JQIamo/RF-Current-Source/Data/D1/D1_422Ohm_20mv_img.PNG

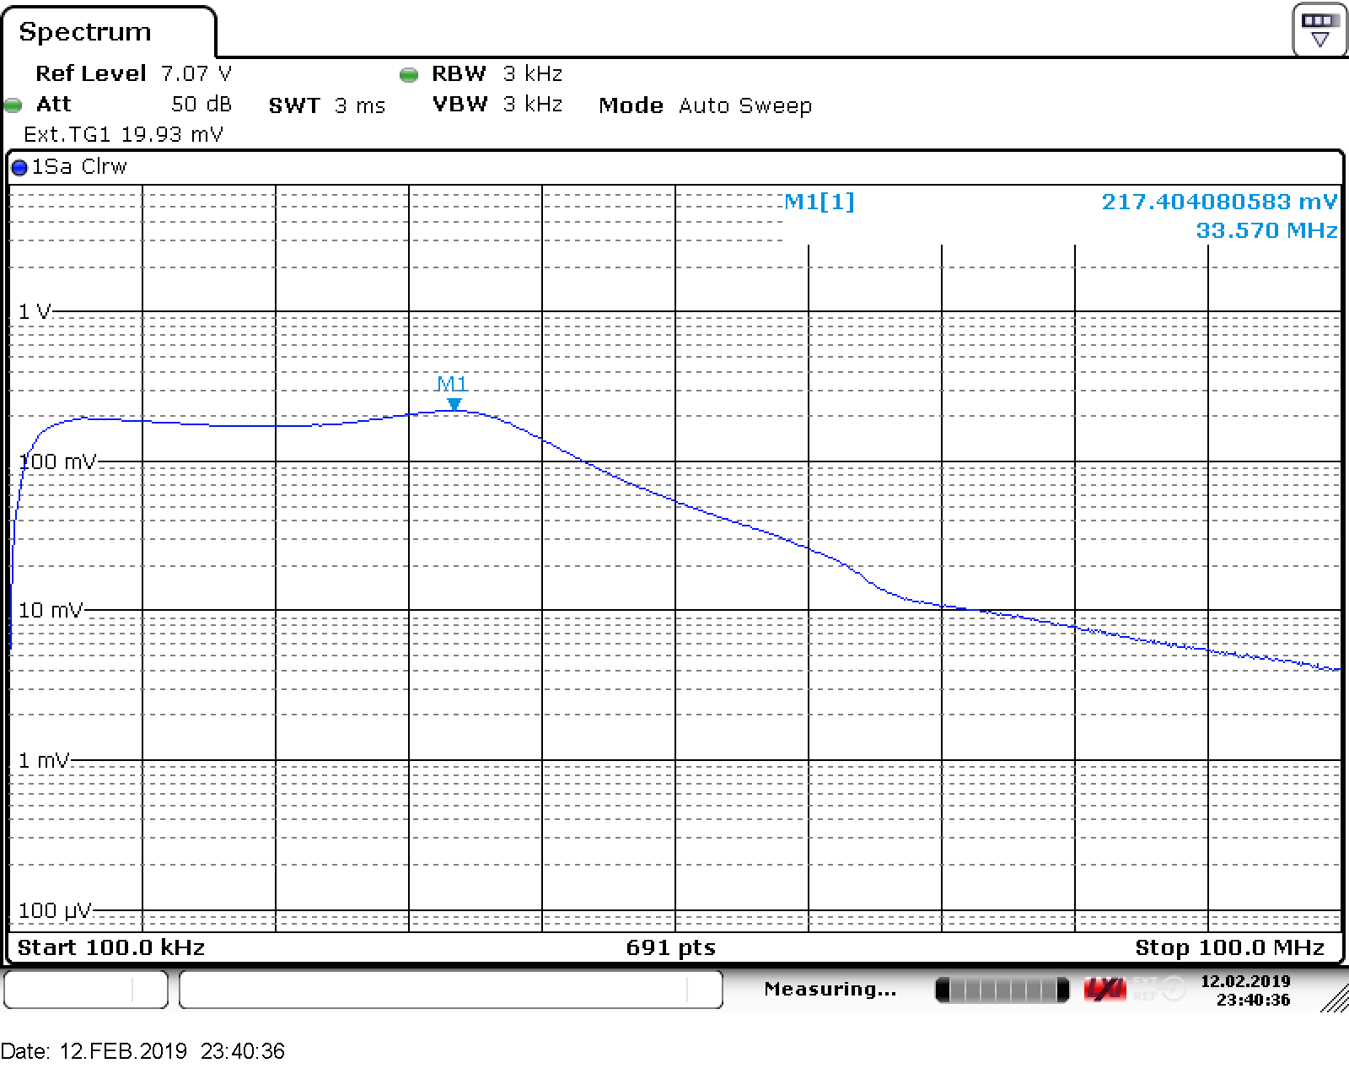
Data/D1/D1_422Ohm_20mv_img.PNG
