JQIamo/RF-Current-Source/Data/D1/D1_422Ohm_50mv_Bitter_img.JPG

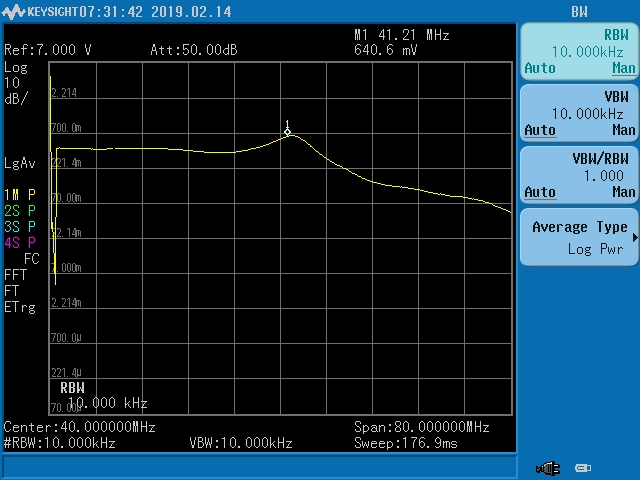
Data/D1/D1_422Ohm_50mv_Bitter_img.JPG
