JQIamo/RF-Current-Source/Data/D1/D1_422Ohm_90mv_img.PNG

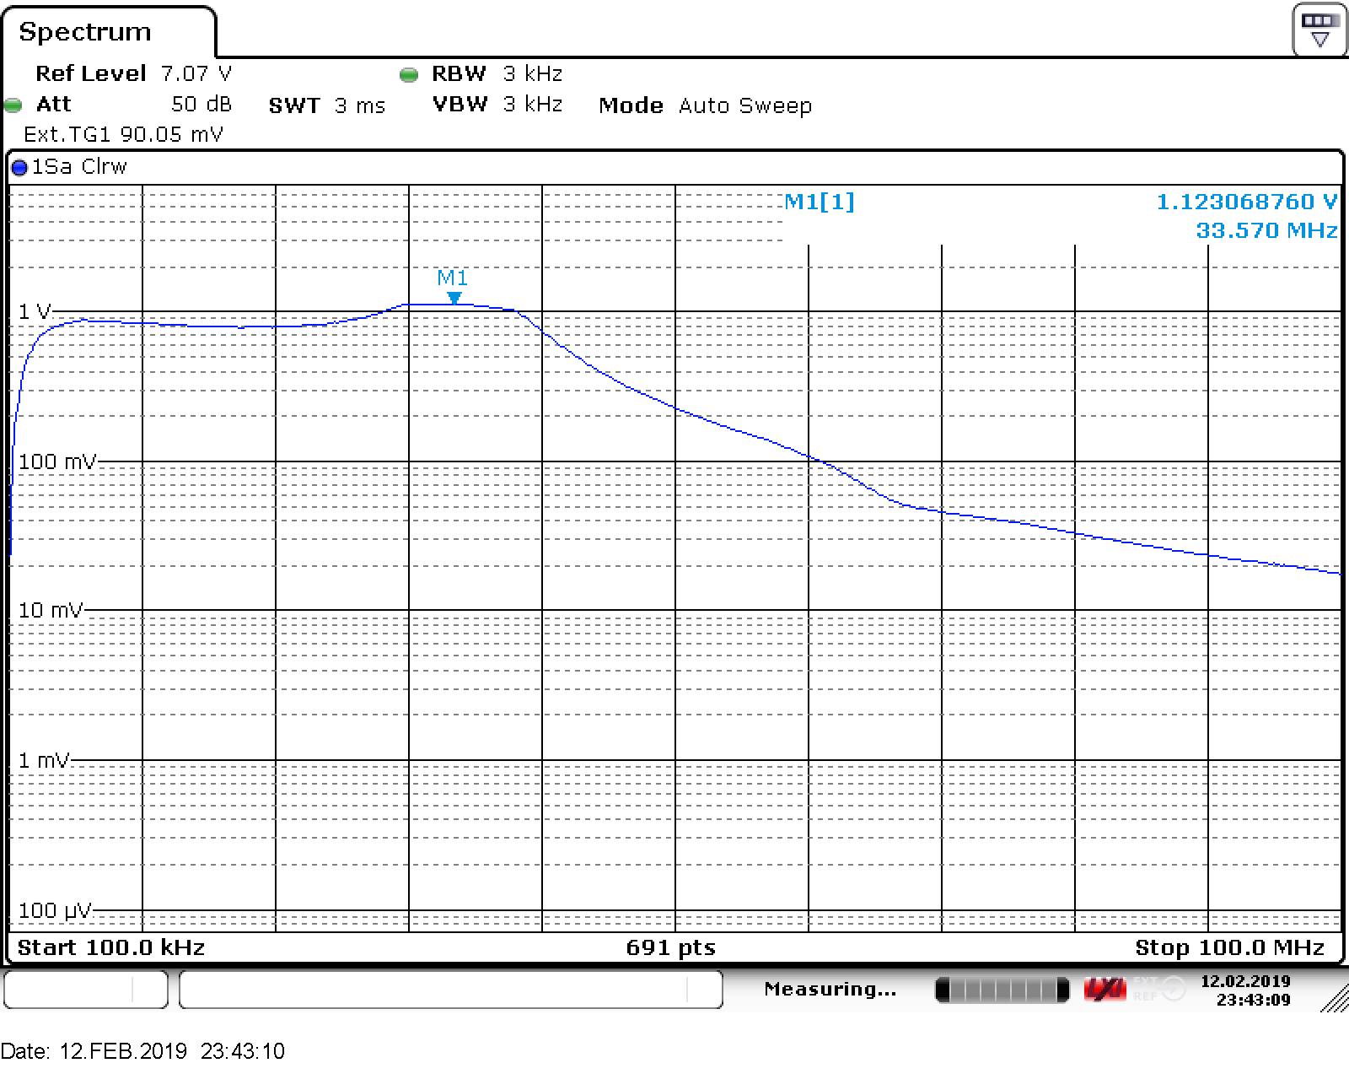
Data/D1/D1_422Ohm_90mv_img.PNG
