JQIamo/RF-Current-Source/Data/D2/D2_422Ohm_20mv_img.PNG

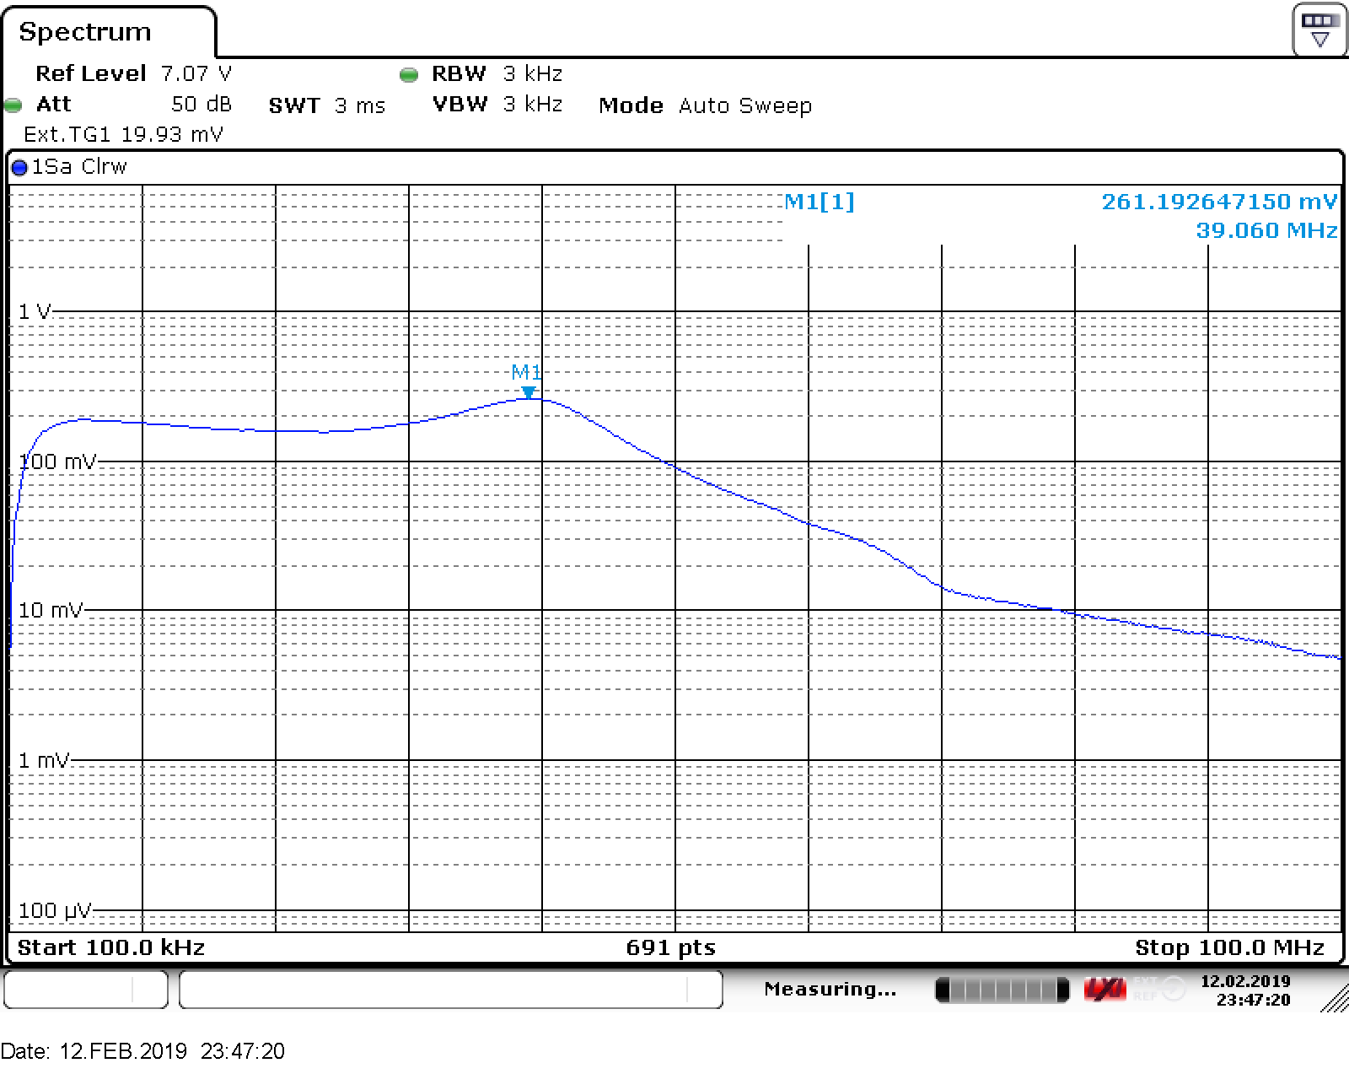
Data/D2/D2_422Ohm_20mv_img.PNG
