JQIamo/RF-Current-Source/Data/Loop/Loop_20mv_120nH_img.PNG

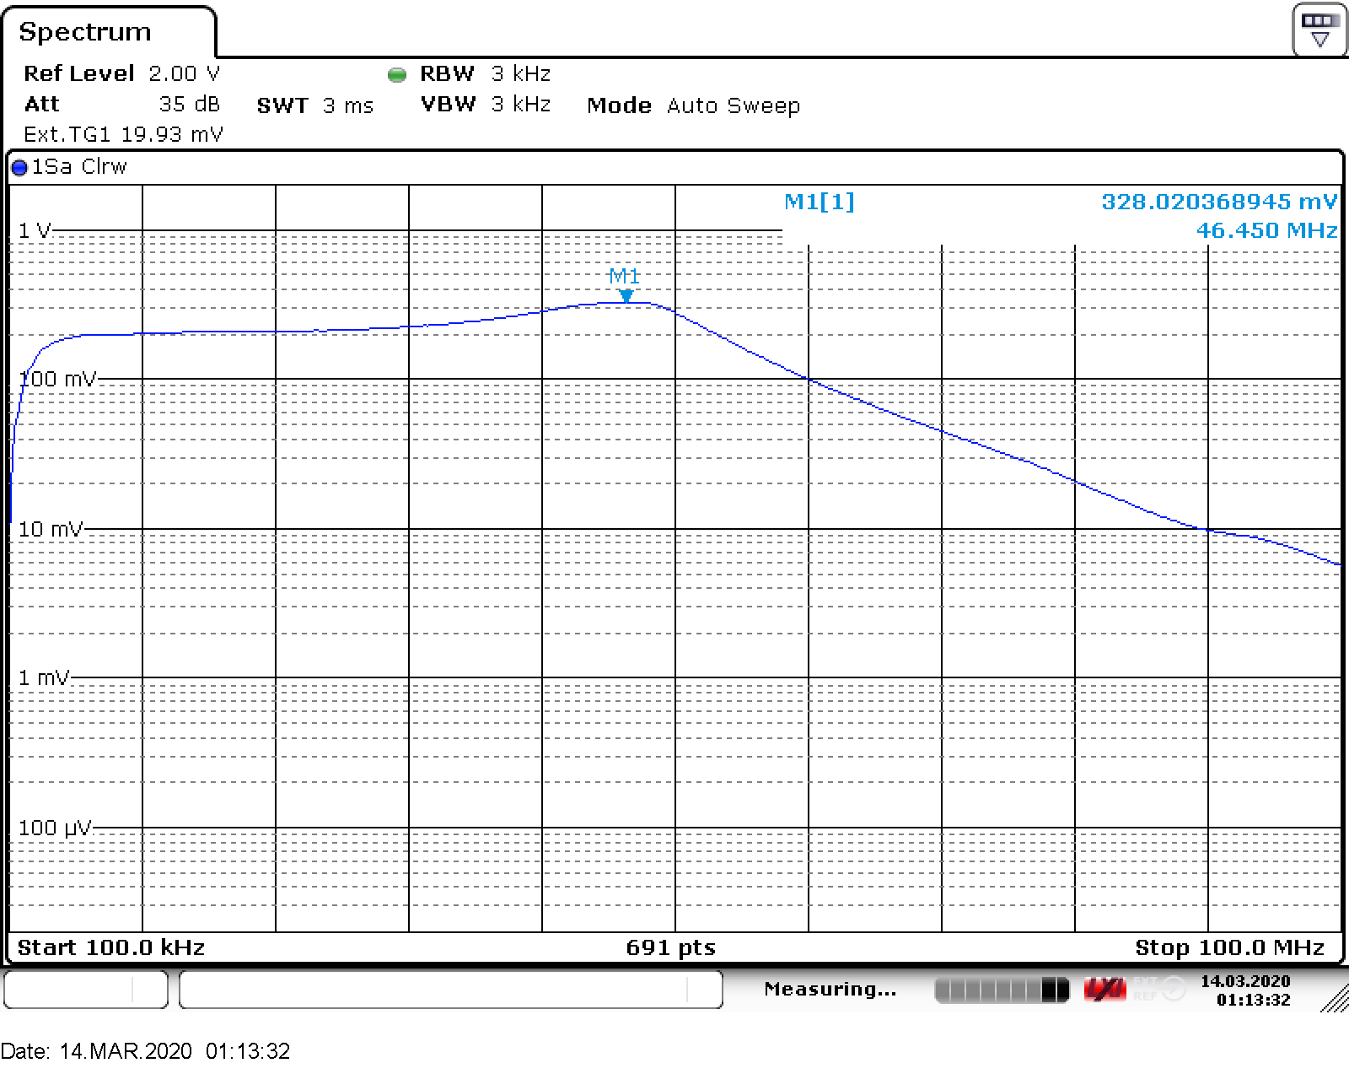
Data/Loop/Loop_20mv_120nH_img.PNG
