JQIamo/RF-Current-Source/Data/Loop/Loop_90mv_120nH_43MHz_img.PNG

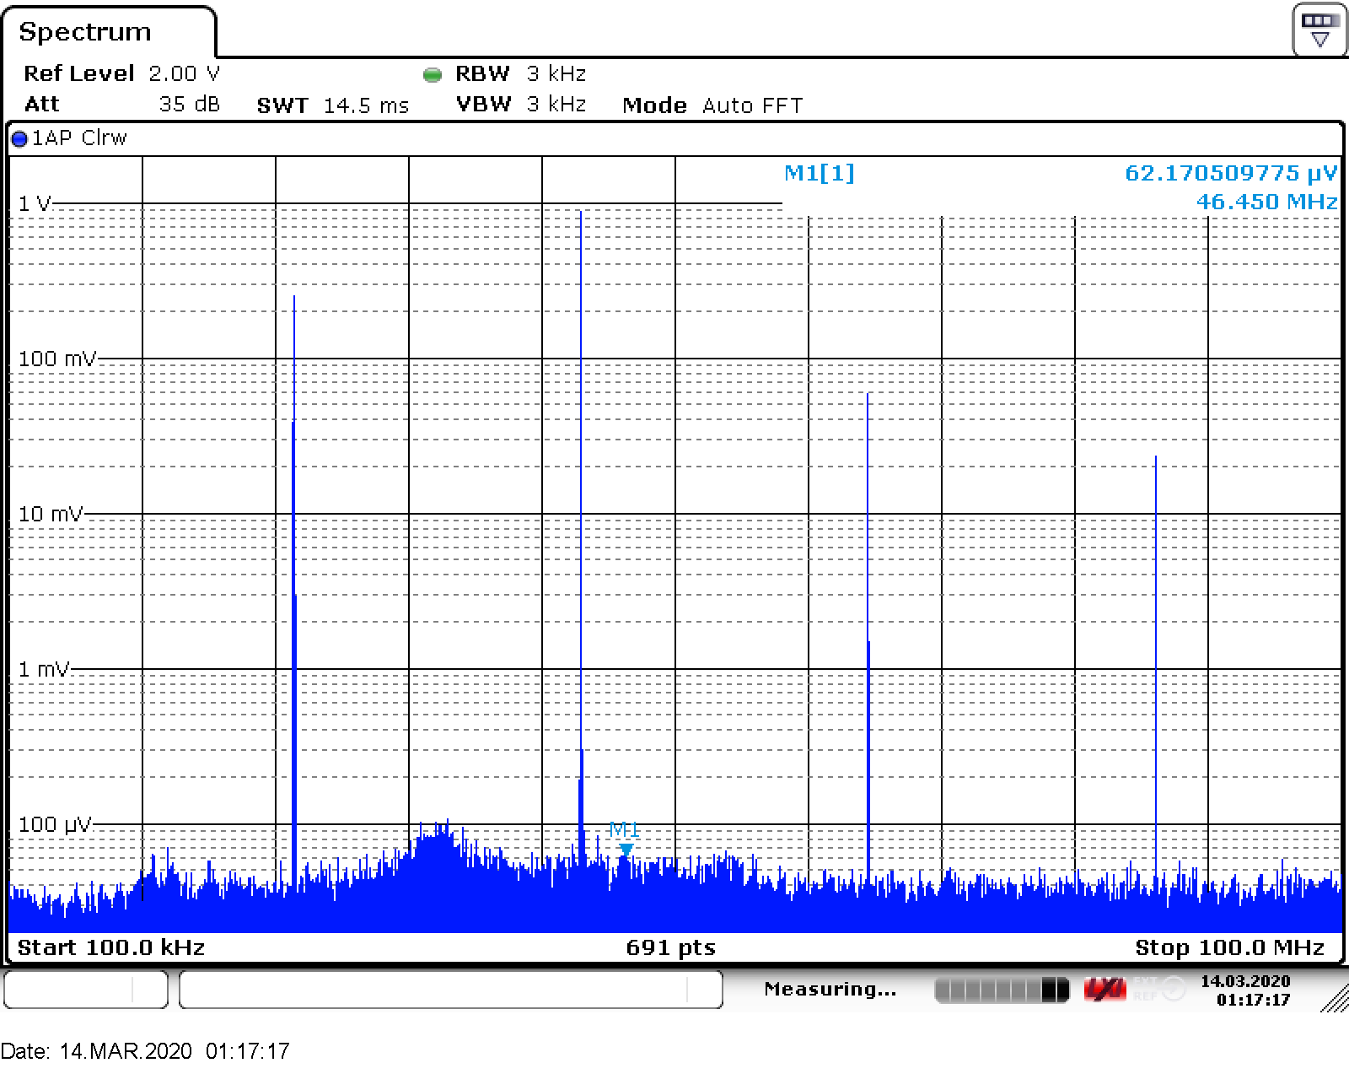
Data/Loop/Loop_90mv_120nH_43MHz_img.PNG
