JQIamo/RF-Current-Source/Data/Loop/loop_215Ohm_10mv_img.PNG

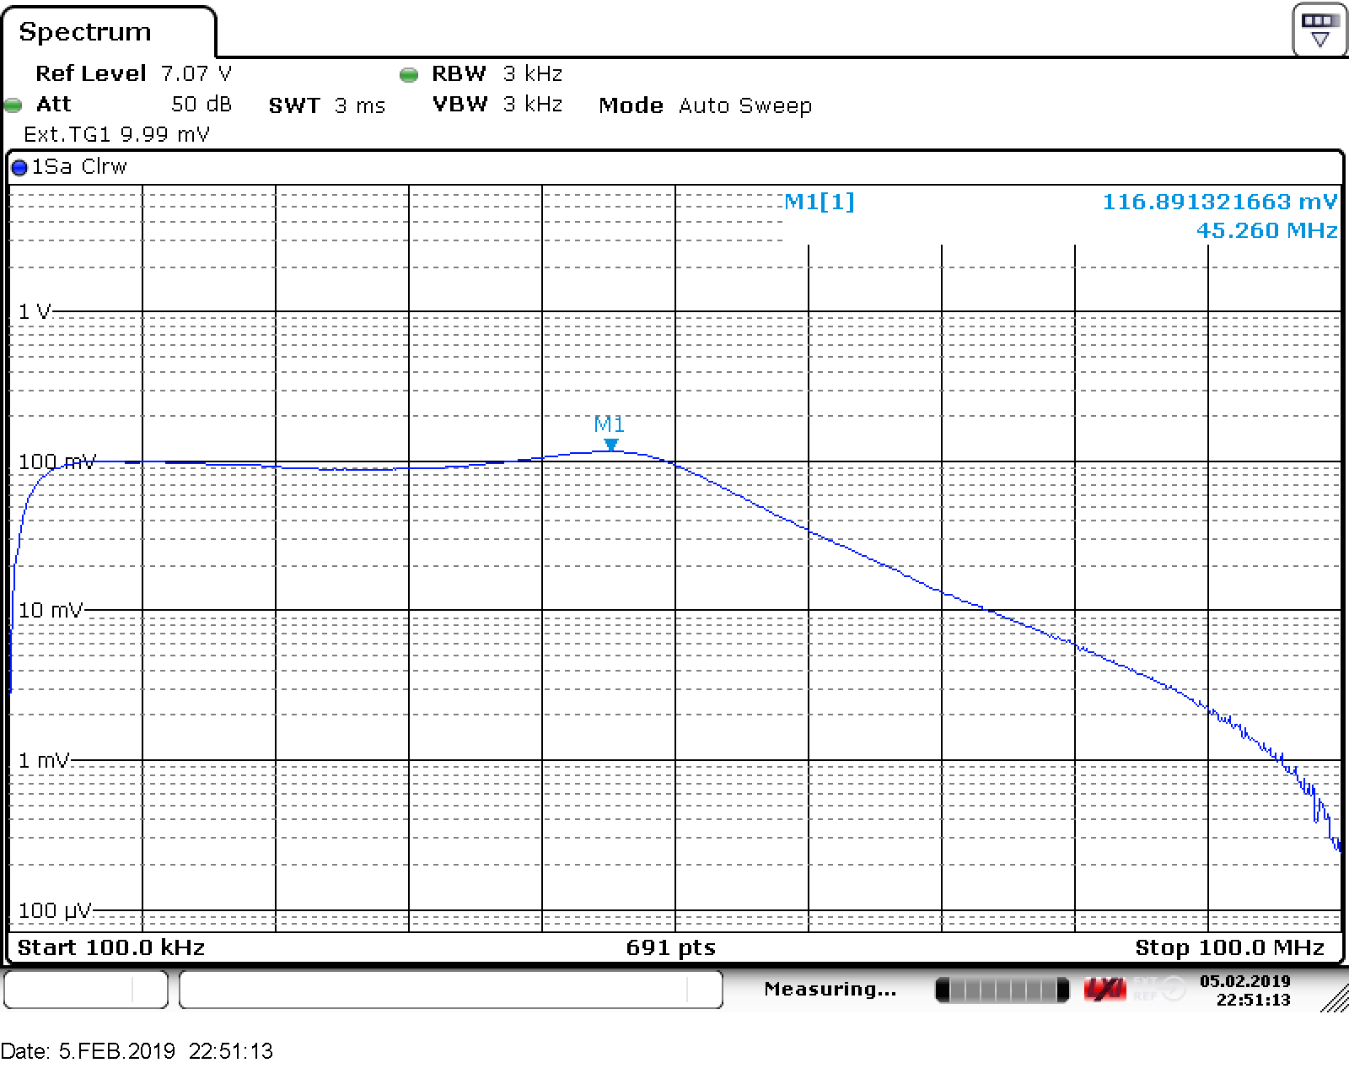
Data/Loop/loop_215Ohm_10mv_img.PNG
