JQIamo/RF-Current-Source/Data/Loop/Loop_215Ohm_20mv_img.PNG

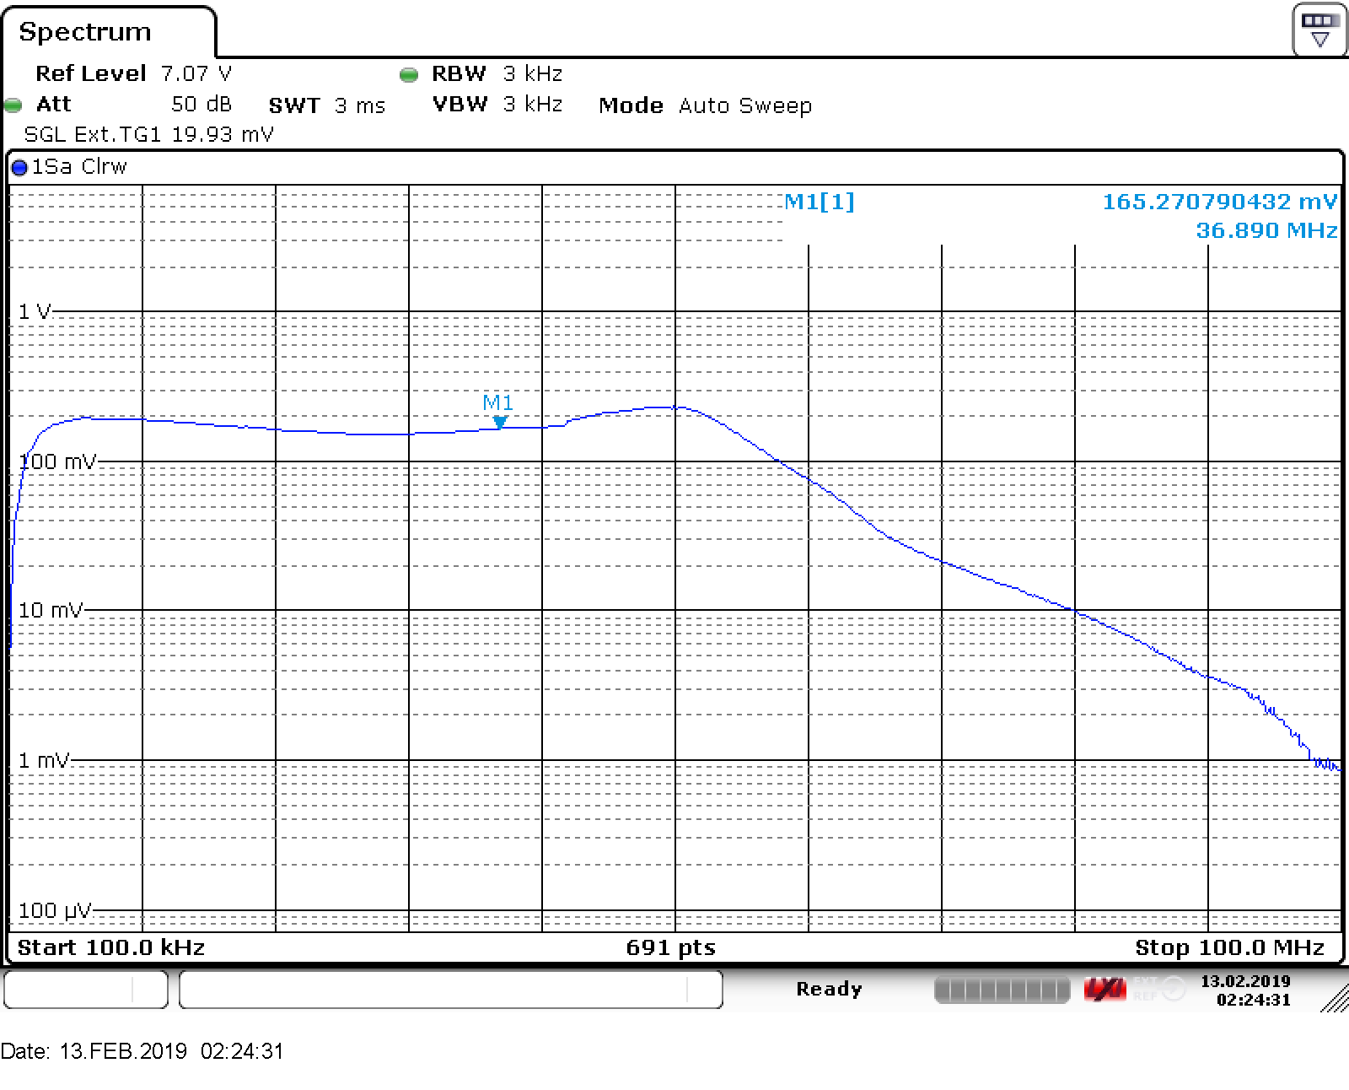
Data/Loop/Loop_215Ohm_20mv_img.PNG
