JQIamo/RF-Current-Source/Data/Simulations/LoopSimParameters.PNG

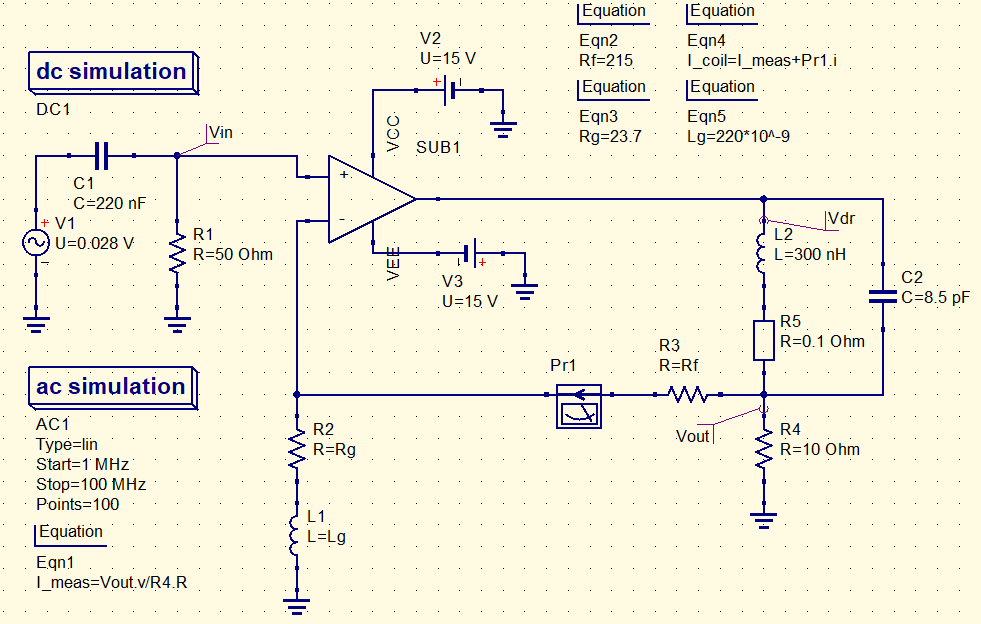
Data/Simulations/LoopSimParameters.PNG
